joachimda/modbus-to-x/software/modbus-to-mqtt/src/network/mbx_server/MBXServer.cpp

#include "network/mbx_server/MBXServer.h"
#include "Logger.h"
#include "constants/HttpResponseCodes.h"
#include "constants/HttpMediaTypes.h"
#include "constants/Routes.h"
#include <ESPAsyncWebServer.h>
#include <SPIFFS.h>
#include <WiFi.h>
#include "Config.h"
#include "storage/ConfigFs.h"
#include "network/NetworkPortal.h"
#include "network/wifi/WifiConfigurationStorage.h"
#include "network/mbx_server/MBXServerHandlers.h"
#include "network/mbx_server/MutationRequestGuardCore.h"
#include "network/mbx_server/OtaRouteRegistration.h"
#include "services/IndicatorService.h"
#include "services/ArduinoOtaManager.h"
#include "services/TimeService.h"
#include "network/mbx_server/OtaRecoveryPage.h"

static constexpr auto WIFI_CONNECT_DELAY_MS = 100;
static constexpr auto WIFI_CONNECT_TIMEOUT = 30000;
static WifiConnectionController g_wifi;

static const char *const CAPTIVE_PORTAL_ENDPOINTS[] = {
    "/generate_204",
    "/gen_204",
    "/hotspot-detect.html",
    "/library/test/success.html",
    "/connecttest.txt",
    "/connecttest",
    "/ncsi.txt",
    "/redirect",
    "/success.txt",
};

MBXServer::MBXServer(AsyncWebServer *server, DNSServer *dnsServer, Logger *logger) : _logger(logger), server(server),
    _dnsServer(dnsServer), _portal(logger, dnsServer) {
}

void MBXServer::begin() {
    ensureConfigFile();
    if (tryConnectWithStoredCreds()) {
        TimeService::requestSync();
        configureRoutes();
        server->begin();
        IndicatorService::instance().setPortalMode(false);
        IndicatorService::instance().setWifiConnected(true);
        ArduinoOtaManager::begin(_logger);
    } else {
        g_wifi.begin(DEFAULT_HOSTNAME);

        MBXServerHandlers::setPortal(&_portal);
        configureAccessPointRoutes();
        server->begin();
        IndicatorService::instance().setPortalMode(true);
        MqttManager::setMQTTEnabled(false);
        _portal.begin([] {
            g_wifi.loop();
        });
    }
}

void MBXServer::loop() {
    MBXServerHandlers::pumpRuntimeResponses();
    g_wifi.loop();
    MBXServerHandlers::pumpEventStream();
    TimeService::loop();
    // Keep LED_A in sync with Wi-Fi status when not in portal mode
    IndicatorService::instance().setWifiConnected(WiFiClass::status() == WL_CONNECTED);
    ArduinoOtaManager::loop();
}

void MBXServer::configureRoutes() const {
    server->serveStatic("/", SPIFFS, Routes::ROOT)
            .setDefaultFile("index.html")
            .setCacheControl("no-store")
            .setFilter([](AsyncWebServerRequest *req) {
                const String &url = req->url();
                return url != Routes::GET_MODBUS_CONFIG && url != Routes::GET_MQTT_CONFIG;
            });

    MBXServerHandlers::initEventStream(server, _logger);

    server->on(Routes::CONFIGURE, HTTP_GET, [this](AsyncWebServerRequest *req) {
        logRequest(req);
        req->send(SPIFFS, "/pages/configure_modbus.html", HttpMediaTypes::HTML);
    });

    server->on(Routes::GET_MODBUS_CONFIG, HTTP_GET, [this](AsyncWebServerRequest *req) {
        logRequest(req);
        serveFsFile(req, ConfigFS, ConfigFs::kModbusConfigFile, nullptr, HttpMediaTypes::JSON, _logger);
    });

    server->on(Routes::GET_MQTT_CONFIG, HTTP_GET, [this](AsyncWebServerRequest *req) {
        logRequest(req);
        serveFsFile(req, ConfigFS, ConfigFs::kMqttConfigFile, nullptr, HttpMediaTypes::JSON, _logger);
    });

    server->on(Routes::GET_MQTT_CONSTRAINTS, HTTP_GET, [this](AsyncWebServerRequest *req) {
        logRequest(req);
        MBXServerHandlers::handleGetMqttConstraints(req);
    });

    server->on(Routes::LOGS, HTTP_GET, [this](AsyncWebServerRequest *req) {
        logRequest(req);
        MBXServerHandlers::getLogs(req);
    });

    server->on(Routes::SYSTEM_STATS, HTTP_GET, [this](AsyncWebServerRequest *req) {
        logRequest(req);
        MBXServerHandlers::getSystemStats(req, _logger);
    });

    server->on(Routes::SYSTEM_READY, HTTP_GET, [](AsyncWebServerRequest *req) {
        MBXServerHandlers::handleSystemReady(req);
    });

    configureMutationRoutes(MutationRouteRegistration::Mode::Station);
    configureOtaRoutes();

    server->onNotFound([this](AsyncWebServerRequest *req) {
        logRequest(req);
        if (!SPIFFS.exists("/index.html")) {
            req->send_P(HttpResponseCodes::OK, HttpMediaTypes::HTML, OTA_RECOVERY_HTML);
            return;
        }
        req->send(HttpResponseCodes::NOT_FOUND, HttpMediaTypes::PLAIN_TEXT, "I haz no file");
    });

}

bool MBXServer::isMutationAllowed(const AsyncWebServerRequest *request) {
    if (request == nullptr) return false;

    const AsyncWebHeader *marker = nullptr;
    size_t markerCount = 0U;
    size_t hostCount = 0U;
    for (size_t i = 0U; i < request->headers(); ++i) {
        const AsyncWebHeader *header = request->getHeader(i);
        if (header != nullptr && header->name().equalsIgnoreCase(MutationRequestGuardCore::REQUEST_HEADER)) {
            marker = header;
            ++markerCount;
        }
        if (header != nullptr && header->name().equalsIgnoreCase("Host")) ++hostCount;
    }
    if (markerCount != 1U || marker == nullptr || hostCount != 1U) return false;

    const String stationIp = WiFi.localIP().toString();
    const String accessPointIp = WiFi.softAPIP().toString();
    return MutationRequestGuardCore::isAllowed(
        marker->value().c_str(), request->host().c_str(), stationIp.c_str(), accessPointIp.c_str(), DEFAULT_HOSTNAME);
}

void MBXServer::configureMutationRoutes(const MutationRouteRegistration::Mode mode) const {
    struct Callbacks {
        const MBXServer *owner;

        bool isMutationAllowed(const AsyncWebServerRequest *request) const {
            return MBXServer::isMutationAllowed(request);
        }

        void sendForbidden(AsyncWebServerRequest *request) const {
            MBXServerHandlers::sendMutationForbidden(request);
        }

        void logRequest(const AsyncWebServerRequest *request) const {
            owner->logRequest(request);
        }

        void handlePutModbusConfigBody(AsyncWebServerRequest *request, const uint8_t *data, const size_t length,
                                       const size_t index, const size_t total) const {
            MBXServerHandlers::handlePutModbusConfigBody(request, data, length, index, total);
        }

        void handlePutMqttConfigBody(AsyncWebServerRequest *request, const uint8_t *data, const size_t length,
                                     const size_t index, const size_t total) const {
            MBXServerHandlers::handlePutMqttConfigBody(request, data, length, index, total);
        }

        void handlePutMqttSecretBody(AsyncWebServerRequest *request, const uint8_t *data, const size_t length,
                                     const size_t index, const size_t total) const {
            MBXServerHandlers::handlePutMqttSecretBody(request, data, length, index, total);
        }

        void handleMqttTestConnection(AsyncWebServerRequest *request) const {
            MBXServerHandlers::handleMqttTestConnection(request);
        }

        void handleModbusExecute(AsyncWebServerRequest *request) const {
            MBXServerHandlers::handleModbusExecute(request);
        }

        void handleModbusDisable(AsyncWebServerRequest *request, const bool state) const {
            MBXServerHandlers::handleModbusDisable(request, state);
        }

        void handleDeviceReset(AsyncWebServerRequest *request) const {
            MBXServerHandlers::handleDeviceReset(request, owner->_logger);
        }

        void handleWifiConnectBody(AsyncWebServerRequest *request, const uint8_t *data, const size_t length,
                                   const size_t index, const size_t total) const {
            MBXServerHandlers::handleWifiConnect(request, g_wifi, data, length, index, total);
        }

        void handleWifiApOff(AsyncWebServerRequest *request) const {
            MBXServerHandlers::handleWifiApOff(request, g_wifi, owner->_logger);
        }

        void handleWifiCancel(AsyncWebServerRequest *request) const {
            MBXServerHandlers::handleWifiCancel(request, g_wifi);
        }

        void handleNetworkReset(AsyncWebServerRequest *request) const {
            MBXServerHandlers::handleNetworkReset(request);
        }
    };

    MutationRouteRegistration::configure<AsyncWebServerRequest>(
        server, Callbacks{this}, mode, HTTP_POST, HTTP_PUT);
}

void MBXServer::configureOtaRoutes() const {
    struct Callbacks {
        const MBXServer *owner;

        bool isAuthorized(const AsyncWebServerRequest *request) const {
            return MBXServerHandlers::isOtaRequestAuthorized(request);
        }

        bool isMutationAllowed(const AsyncWebServerRequest *request) const {
            return MBXServer::isMutationAllowed(request);
        }

        bool cacheUploadAuthorization(AsyncWebServerRequest *request) const {
            return MBXServerHandlers::cacheOtaUploadAuthorization(request);
        }

        void sendUnauthorized(AsyncWebServerRequest *request) const {
            MBXServerHandlers::sendOtaUnauthorized(request);
        }

        void sendForbidden(AsyncWebServerRequest *request) const {
            MBXServerHandlers::sendMutationForbidden(request);
        }

        void logRequest(const AsyncWebServerRequest *request) const {
            owner->logRequest(request);
        }

        void handleFirmwareUpload(AsyncWebServerRequest *request, const String &filename, const size_t index,
                                  uint8_t *data, const size_t length, const bool final) const {
            MBXServerHandlers::handleOtaFirmwareUpload(
                request, filename, index, data, length, final, owner->_logger);
        }

        void handleFilesystemUpload(AsyncWebServerRequest *request, const String &filename, const size_t index,
                                    uint8_t *data, const size_t length, const bool final) const {
            MBXServerHandlers::handleOtaFilesystemUpload(
                request, filename, index, data, length, final, owner->_logger);
        }

        void handleHttpCheck(AsyncWebServerRequest *request) const {
            MBXServerHandlers::handleOtaHttpCheck(request, owner->_logger);
        }

        void handleHttpNotes(AsyncWebServerRequest *request) const {
            MBXServerHandlers::handleOtaHttpNotes(request, owner->_logger);
        }

        void handleHttpApply(AsyncWebServerRequest *request) const {
            MBXServerHandlers::handleOtaHttpApply(request, owner->_logger);
        }

        void handleGetHttpSettings(AsyncWebServerRequest *request) const {
            MBXServerHandlers::handleGetOtaHttpSettings(request);
        }

        void handlePutHttpSettingsBody(AsyncWebServerRequest *request, const uint8_t *data, const size_t length,
                                       const size_t index, const size_t total) const {
            MBXServerHandlers::handlePutOtaHttpSettingsBody(request, data, length, index, total);
        }

        void handlePutPasswordBody(AsyncWebServerRequest *request, const uint8_t *data, const size_t length,
                                   const size_t index, const size_t total) const {
            MBXServerHandlers::handlePutOtaPasswordBody(request, data, length, index, total);
        }

        void handleDeletePassword(AsyncWebServerRequest *request) const {
            MBXServerHandlers::handleDeleteOtaPassword(request);
        }

        void handleFactoryResetBody(AsyncWebServerRequest *request, const uint8_t *data, const size_t length,
                                    const size_t index, const size_t total) const {
            MBXServerHandlers::handleFactoryResetBody(request, data, length, index, total, owner->_logger);
        }
    };

    OtaRouteRegistration::configure<AsyncWebServerRequest, String>(
        server, Callbacks{this}, HTTP_GET, HTTP_POST, HTTP_PUT, HTTP_DELETE);
}

void MBXServer::configureAccessPointRoutes() const {
    server->serveStatic("/", SPIFFS, "/")
            .setDefaultFile("/pages/mbx_captive_portal.html")
            .setCacheControl("no-store")
            .setFilter([](AsyncWebServerRequest *req) {
                const String &url = req->url();
                return url != Routes::GET_MODBUS_CONFIG && url != Routes::GET_MQTT_CONFIG;
            });

    server->on(Routes::ROOT, HTTP_GET, [this](AsyncWebServerRequest *req) {
        if (!SPIFFS.exists("/pages/mbx_captive_portal.html")) {
            req->send(HttpResponseCodes::OK, HttpMediaTypes::HTML, OTA_RECOVERY_HTML);
            return;
        }
        serveFsFile(req, SPIFFS, "/pages/mbx_captive_portal.html", nullptr, HttpMediaTypes::HTML, _logger);
    });

    server->on(Routes::GET_SSID_LIST, HTTP_GET, [](AsyncWebServerRequest *req) {
        MBXServerHandlers::getSsidListAsJson(req);
    });

    server->on(Routes::GET_WIFI_STATUS, HTTP_GET, [this](AsyncWebServerRequest *req) {
        logRequest(req);
        MBXServerHandlers::handleWifiStatus(req, g_wifi);
    });
    configureMutationRoutes(MutationRouteRegistration::Mode::AccessPoint);
    configureOtaRoutes();

    for (const char *path : CAPTIVE_PORTAL_ENDPOINTS) {
        server->on(path, HTTP_ANY, [](AsyncWebServerRequest *req) {
            MBXServerHandlers::handleCaptivePortalRedirect(req);
        });
    }

    server->onNotFound([](AsyncWebServerRequest *req) {
        if (!SPIFFS.exists("/pages/mbx_captive_portal.html")) {
            req->send(HttpResponseCodes::OK, HttpMediaTypes::HTML, OTA_RECOVERY_HTML);
            return;
        }
        MBXServerHandlers::handleCaptivePortalRedirect(req);
    });
}

auto MBXServer::accessPointFilter(AsyncWebServerRequest *request) -> bool {
    // True when the HTTP connection is to this AP interface,
    const IPAddress dest = request->client()->localIP();
    return dest == WiFi.softAPIP();
}

auto MBXServer::tryConnectWithStoredCreds() const -> bool {
    if (WiFiClass::getMode() != WIFI_MODE_STA) {
        WiFiClass::mode(WIFI_MODE_STA);
        delay(300);
    }

    WiFi.persistent(false);
    WiFiClass::setHostname(DEFAULT_HOSTNAME);

    WifiStaticConfig staticConfiguration;
    const auto storedConfiguration = WifiConfigurationStorage::load(staticConfiguration);
    if (storedConfiguration == WifiConfigurationStorage::LoadResult::Unavailable
        || storedConfiguration == WifiConfigurationStorage::LoadResult::Invalid) {
        _logger->logError("Stored IPv4 configuration is unavailable or invalid");
        return false;
    }

    bool addressingConfigured = false;
    if (storedConfiguration == WifiConfigurationStorage::LoadResult::Static) {
        IPAddress ip;
        IPAddress gateway;
        IPAddress subnet;
        IPAddress dns1;
        IPAddress dns2;
        const bool parsed = ip.fromString(staticConfiguration.ip)
                            && gateway.fromString(staticConfiguration.gateway)
                            && subnet.fromString(staticConfiguration.subnet)
                            && (!staticConfiguration.dns1.length() || dns1.fromString(staticConfiguration.dns1))
                            && (!staticConfiguration.dns2.length() || dns2.fromString(staticConfiguration.dns2));
        addressingConfigured = parsed && WiFi.config(ip, gateway, subnet, dns1, dns2);
    } else {
        addressingConfigured = WiFi.config(INADDR_NONE, INADDR_NONE, INADDR_NONE);
    }
    if (!addressingConfigured) {
        _logger->logError("Failed to apply stored IPv4 configuration");
        return false;
    }

    WiFi.begin();

    const unsigned long start = millis();
    while (millis() - start < WIFI_CONNECT_TIMEOUT) {
        if (WiFiClass::status() == WL_CONNECTED) {
            _logger->logInformation(("Connected to WiFi: " + WiFi.SSID() +
                                     " " + WiFi.localIP().toString()).c_str());
            return true;
        }
        delay(WIFI_CONNECT_DELAY_MS);
    }
    _logger->logInformation(
        "MBXServer::tryConnectWithStoredCreds() - No connection with stored credentials; starting AP portal");
    return false;
}

void MBXServer::serveFsFile(AsyncWebServerRequest *reqPtr, FS &fs, const char *path,
                            const std::function<void()> &onServed, const char *contentType, const Logger *logger) {
    if (fs.exists(path)) {
        logger->logDebug(("Serving file: " + String(path)).c_str());
        reqPtr->send(fs, path, contentType);
        if (onServed) {
            reqPtr->onDisconnect([onServed] {
                onServed();
            });
        }
    } else {
        logger->logDebug(("File not found: " + String(path)).c_str());
        reqPtr->send(HttpResponseCodes::NOT_FOUND, HttpMediaTypes::PLAIN_TEXT, "Page not found");
    }
}

void MBXServer::logRequest(const AsyncWebServerRequest *request) const {
    _logger->logDebug(
        ("MBXServer: - Processing request: " + String(request->methodToString()) + ": " + String(request->url())).
        c_str());
}

void MBXServer::ensureConfigFile() const {
    if (!ConfigFS.exists(ConfigFs::kModbusConfigFile)) {
        _logger->logWarning("MBXServer::ensureConfigFile - Config file not found. Creating new one");

        File file = ConfigFS.open(ConfigFs::kModbusConfigFile, FILE_WRITE);
        if (!file) {
            return;
        }

        file.print("{}");
        file.close();
    }

    if (!ConfigFS.exists(ConfigFs::kMqttConfigFile)) {
        _logger->logWarning("MBXServer::ensureConfigFile - MQTT config file not found. Creating new one");
        File file = ConfigFS.open(ConfigFs::kMqttConfigFile, FILE_WRITE);
        if (file) {
            file.print(R"({"enabled":false,"broker_ip":"0.0.0.0","broker_url":"","broker_port":"1883","user":"","root_topic":"mbx_root"})");
            file.close();
        }
    }
}

auto MBXServer::safeWriteFile(FS &fs, const char *path, const String &content) -> bool {
    const String tmp = String(path) + ".tmp";
    File f = fs.open(tmp, FILE_WRITE);
    if (!f) {
        return false;
    }
    const size_t n = f.print(content);

    f.flush();
    f.close();
    if (n != content.length()) {
        fs.remove(tmp);
        return false;
    }
    fs.remove(path);
    return fs.rename(tmp, path);
}

auto MBXServer::readConfig() const -> String {
    if (!ConfigFS.exists(ConfigFs::kModbusConfigFile)) {
        _logger->logError("MBXServer::readConfig - File System error");
        return "{}";
    }

    File file = ConfigFS.open(ConfigFs::kModbusConfigFile, FILE_READ);
    String json = file.readString();
    file.close();
    return json;
}

void MBXServer::streamSPIFFSFileChunked(AsyncWebServerRequest *req, const char *path, const char *contentType) {
    if (!SPIFFS.exists(path)) {
        req->send(HttpResponseCodes::NOT_FOUND, HttpMediaTypes::PLAIN_TEXT, "Page not found");
        return;
    }

    auto filePtr = std::make_shared<File>(SPIFFS.open(path, FILE_READ));
    if (!filePtr || !(*filePtr)) {
        req->send(HttpResponseCodes::INTERNAL_SERVER_ERROR, HttpMediaTypes::PLAIN_TEXT, "File open failed");
        return;
    }

    auto *response = req->beginChunkedResponse(contentType,
                                               [filePtr](uint8_t *buffer, const size_t maxLen, size_t) -> size_t {
                                                   if (!*filePtr) return 0;
                                                   const size_t n = filePtr->read(buffer, maxLen);
                                                   // Returning 0 signals end-of-stream; shared_ptr will release and close
                                                   return n;
                                               });

    response->addHeader("Cache-Control", "no-store");
    req->send(response);
}
