joachimda/modbus-to-x/software/modbus-to-mqtt/src/services/ArduinoOtaManager.cpp

#include "services/ArduinoOtaManager.h"
#if DEV_OTA_ENABLED
#include <ArduinoOTA.h>
#include "services/IndicatorService.h"
#include "Logger.h"

static Logger *g_logger = nullptr;
static bool g_started = false;

void ArduinoOtaManager::begin(Logger *logger) {
    if (DEV_OTA_ARDUINO_PASS[0] == '\0') {
        if (logger) logger->logWarning("Dev-OTA disabled: no local password supplied");
        return;
    }
    g_logger = logger;

    ArduinoOTA
        .onStart([] {
            IndicatorService::instance().setOtaActive(true);
            if (g_logger) g_logger->logInformation("Dev-OTA: Start");
        })
        .onEnd([] {
            IndicatorService::instance().setOtaActive(false);
            if (g_logger) g_logger->logInformation("Dev-OTA: End");
        })
        .onProgress([](const unsigned int progress, const unsigned int total) {
            (void)progress; (void)total;
        })
        .onError([](const ota_error_t error) {
            if (g_logger) g_logger->logError((String("ArduinoOTA Error: ") + String(error)).c_str());
        });

    ArduinoOTA.setPassword(DEV_OTA_ARDUINO_PASS);
    ArduinoOTA.setPartitionLabel("spiffs");
    ArduinoOTA.begin();
    g_started = true;
    if (g_logger) g_logger->logInformation("Dev-OTA: Ready");
}

void ArduinoOtaManager::loop() {
    if (g_started) ArduinoOTA.handle();
}
#else
void ArduinoOtaManager::begin(Logger *) {}
void ArduinoOtaManager::loop() {}
#endif
